hagen-gloetter/KBS/display/16x2_Display_test.py

#! /usr/bin/python3
# -*- coding: utf-8 -*-
#
# KBS – LCD Display Test
# Einfacher Hardware-Test: Zeigt Text an und blinkt das Backlight.
# Dient zur Ueberpruefung der I2C-Verbindung und Display-Funktion.
#

import lcddriver
import time
lcd = lcddriver.lcd()

lcd.lcd_clear()
lcd.lcd_backlight("on")

lcd.lcd_display_string("Ramona",1)
lcd.lcd_display_string("Hagen",2)

time.sleep(1)
lcd.lcd_backlight("on")
time.sleep(1)
lcd.lcd_backlight("off")
time.sleep(1)
lcd.lcd_backlight("on")
time.sleep(1)
lcd.lcd_backlight("off")
time.sleep(1)
lcd.lcd_backlight("on")
time.sleep(1)
lcd.lcd_backlight("off")
time.sleep(1)
lcd.lcd_backlight("on")
time.sleep(1)
